vacmor119/Automatic-Greenhouse/images/blokovy_diagram_cs.drawio.png

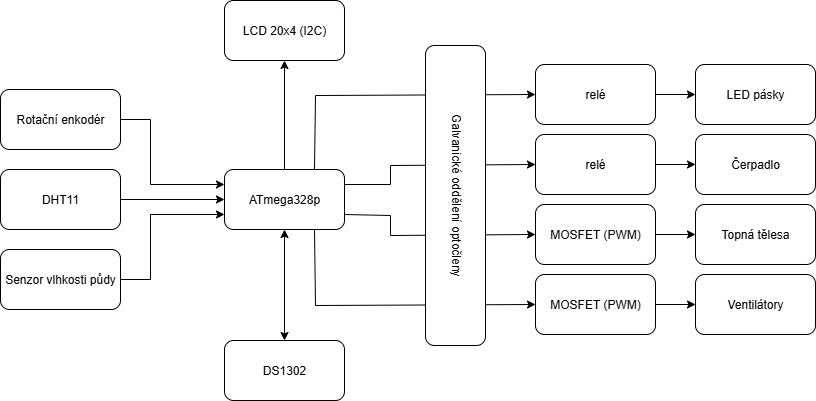
images/blokovy_diagram_cs.drawio.png
