vacmor119/Automatic-Greenhouse/images/blokovy_diagram_en.png

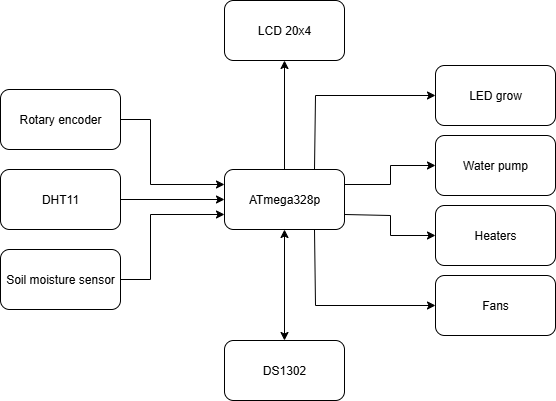
images/blokovy_diagram_en.png
