vacmor119/Automatic-Greenhouse/images/spinani_mosfetu_s_TLP250/filtr_kondik_jen_na_napajeni.bmp

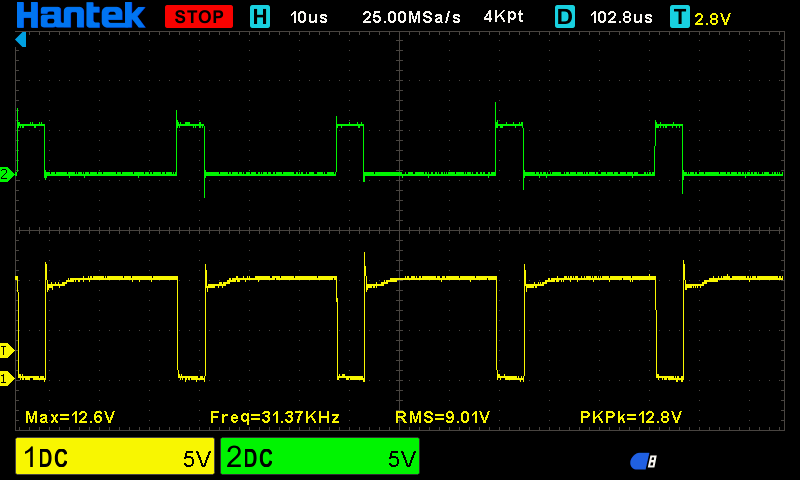
images/spinani_mosfetu_s_TLP250/filtr_kondik_jen_na_napajeni.bmp
