vacmor119/Automatic-Greenhouse/images/spinani_mosfetu_s_TLP250/napetova_spicka.bmp

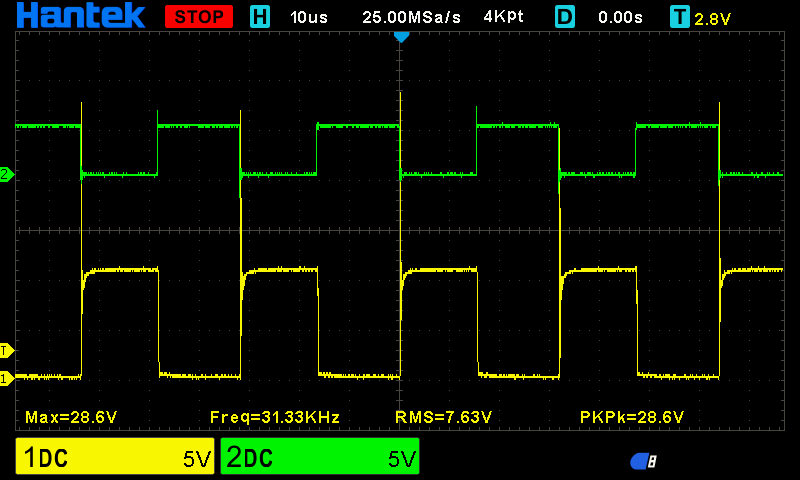
images/spinani_mosfetu_s_TLP250/napetova_spicka.bmp
