vacmor119/Automatic-Greenhouse/images/spinani_mosfetu_s_TLP250/napetova_spicka_closeup2.bmp

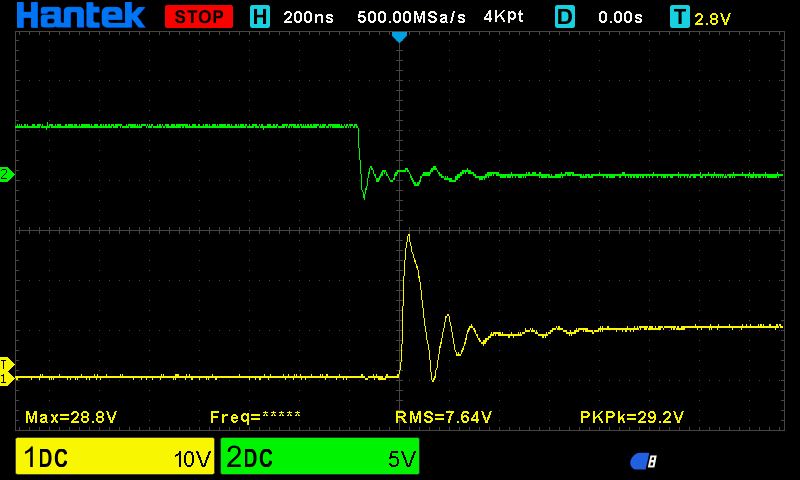
images/spinani_mosfetu_s_TLP250/napetova_spicka_closeup2.bmp
