vacmor119/Automatic-Greenhouse/images/vizualizace/pohled2.png

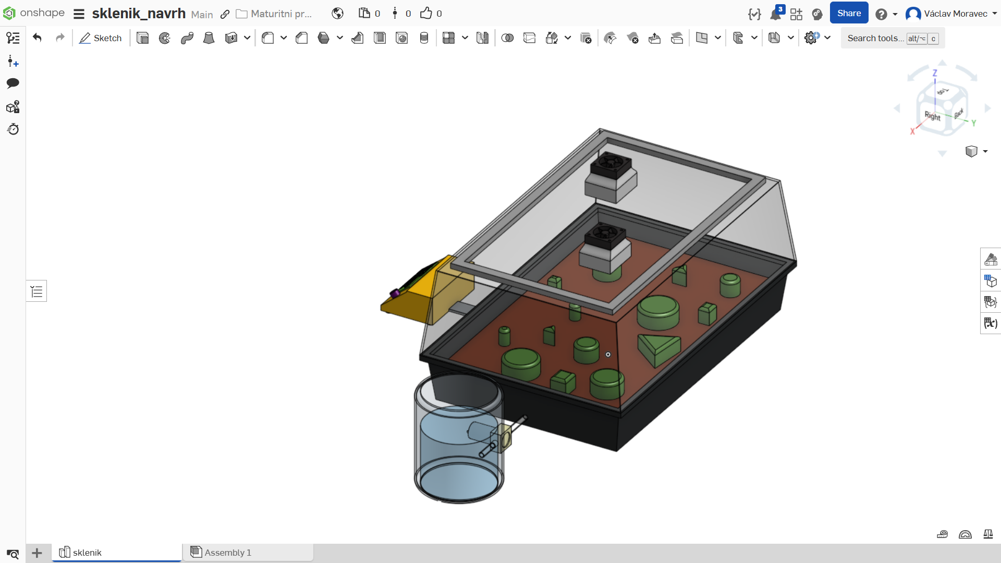
images/vizualizace/pohled2.png
