vacmor119/Automatic-Greenhouse/images/vizualizace/pohled3.png

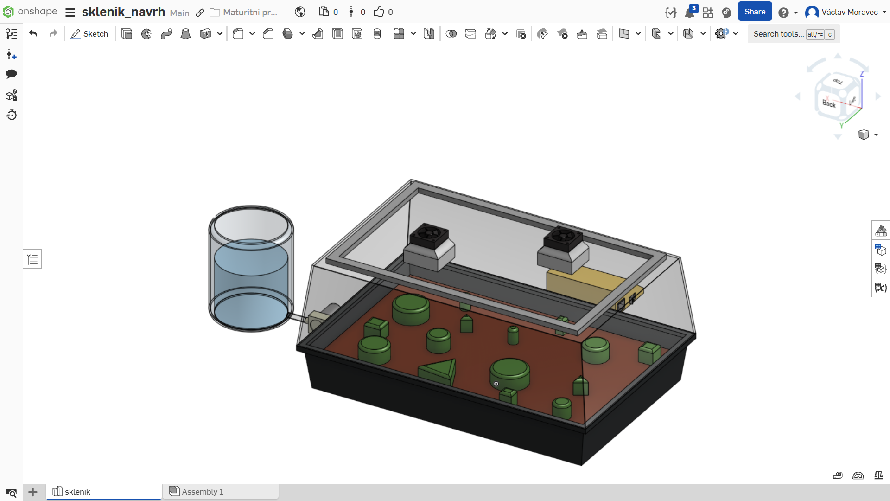
images/vizualizace/pohled3.png
