vacmor119/Automatic-Greenhouse/images/vizualizace/pohled4.png

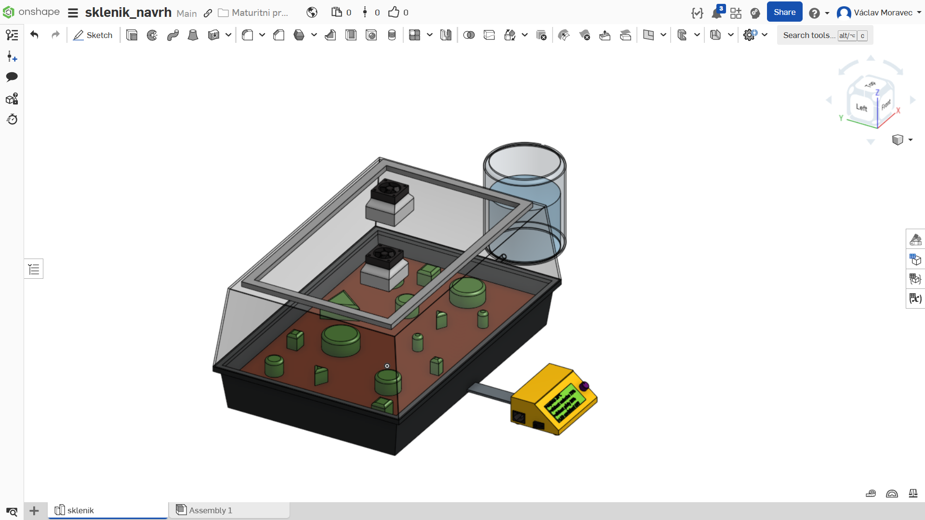
images/vizualizace/pohled4.png
