vacmor119/Automatic-Greenhouse/PCB/hrubý_návrh.png

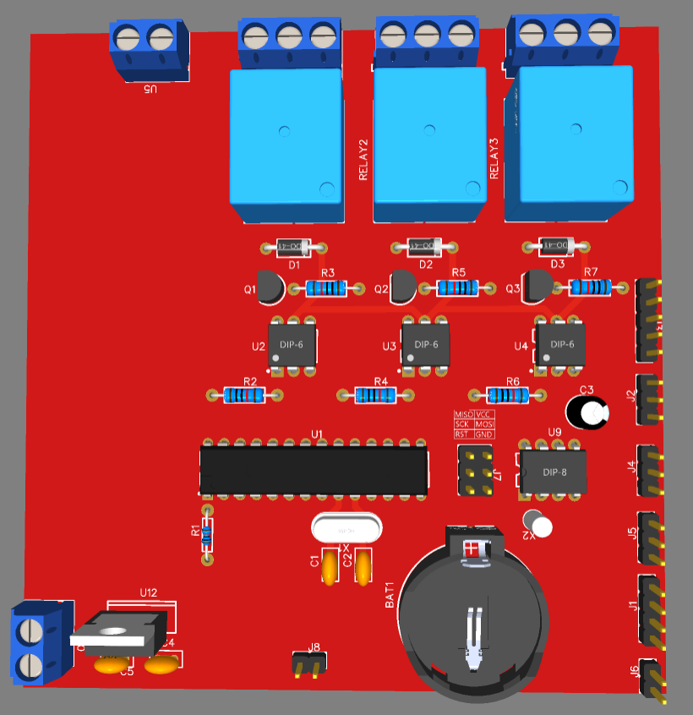
PCB/hrubý_návrh.png
